EnemyoftheFarmer/DC-programmable-load/Eload-Horizon/Electronic-Load/pool/3d_models/cache/6d752bc3-29b3-45df-8cf2-1e3aacefbcc6/3d_models/connector/header/2.54mm/PinHeader_2x06_P2.54mm_Vertical.step

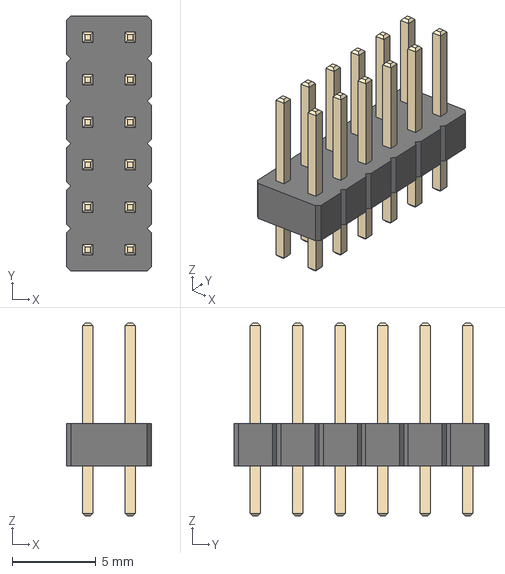
[picture p18: CAD file, 2022-11-15]
Eload-Horizon/Electronic-Load/pool/3d_models/cache/6d752bc3-29b3-45df-8cf2-1e3aacefbcc6/3d_models/connector/header/2.54mm/PinHeader_2x06_P2.54mm_Vertical.step
5.08 x 15.2 x 11.5 mm
