EnemyoftheFarmer/DC-programmable-load/Eload-Horizon/Electronic-Load/pool/3d_models/Mill-Max/mill-max-380-10-102-00-001000.STEP

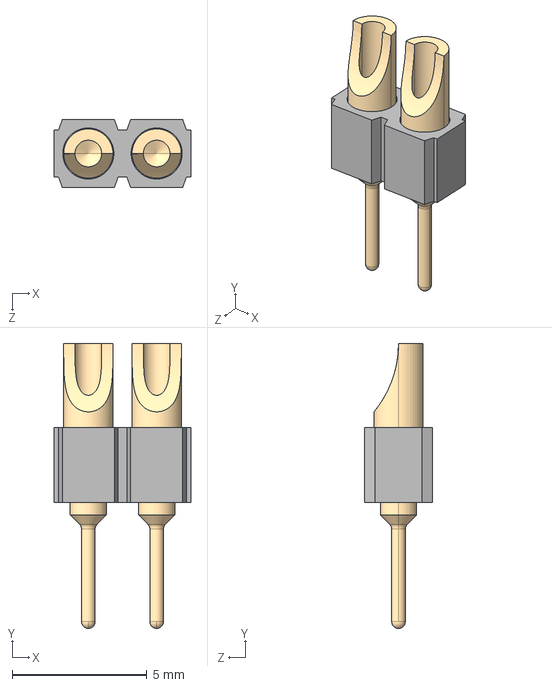
[picture p20: CAD file, 2022-11-15]
Eload-Horizon/Electronic-Load/pool/3d_models/Mill-Max/mill-max-380-10-102-00-001000.STEP
5.08 x 10.6 x 2.54 mm
P3XX-11-010-00-000000_P302-11-010-00-000000
