EnemyoftheFarmer/DC-programmable-load/Eload-Horizon/Electronic-Load/pool/3d_models/Vishay/thjp_3dmodels/THJP1206A.stp

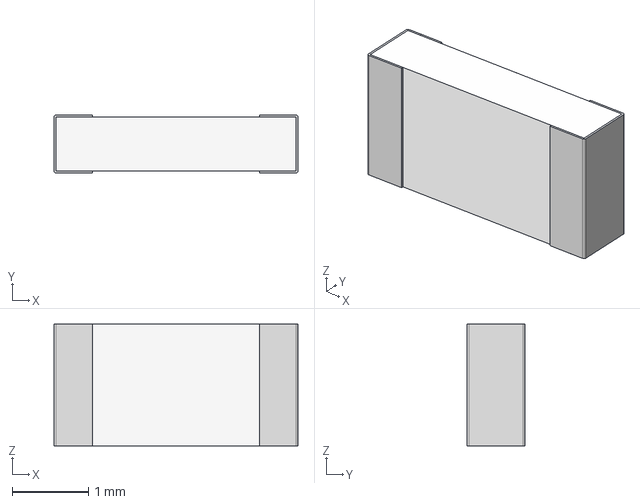
[picture p21: CAD file, 2022-04-26]
Eload-Horizon/Electronic-Load/pool/3d_models/Vishay/thjp_3dmodels/THJP1206A.stp
3.20 x 0.762 x 1.60 mm
