EnemyoftheFarmer/DC-programmable-load/Eload-Horizon/Electronic-Load/pool/3d_models/Vishay/WSL2010...18 (0.001 to 0.0069).STEP

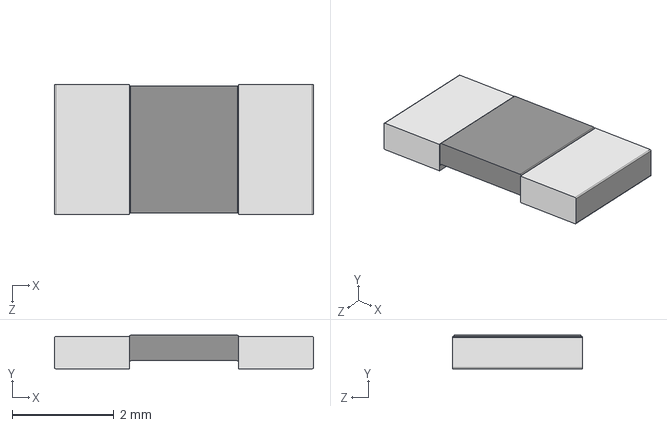
[picture p22: CAD file, 2022-04-26]
Eload-Horizon/Electronic-Load/pool/3d_models/Vishay/WSL2010...18 (0.001 to 0.0069).STEP
5.08 x 0.66 x 2.54 mm
