EnemyoftheFarmer/DC-programmable-load/Eload-Horizon/Controller/pool/3d_models/cache/6d752bc3-29b3-45df-8cf2-1e3aacefbcc6/3d_models/connector/header/2.54mm/PinHeader_1x04_P2.54mm_Vertical.step

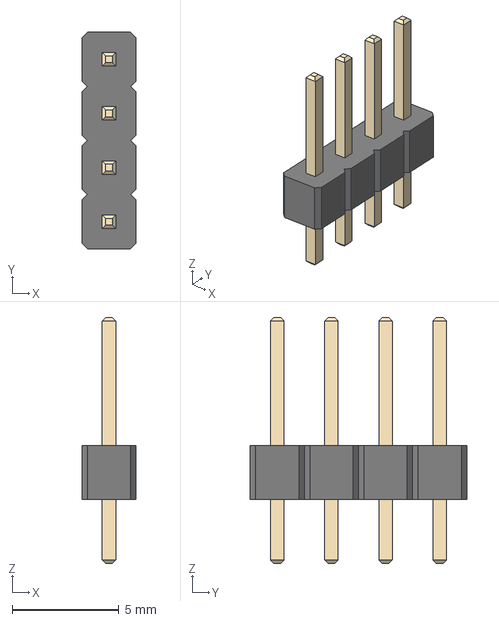
[picture p24: CAD file, 2022-11-15]
Eload-Horizon/Controller/pool/3d_models/cache/6d752bc3-29b3-45df-8cf2-1e3aacefbcc6/3d_models/connector/header/2.54mm/PinHeader_1x04_P2.54mm_Vertical.step
2.54 x 10.2 x 11.5 mm
