EnemyoftheFarmer/DC-programmable-load/Eload-Horizon/Electronic-Load/pool/3d_models/Vishay/RS1-2.STEP

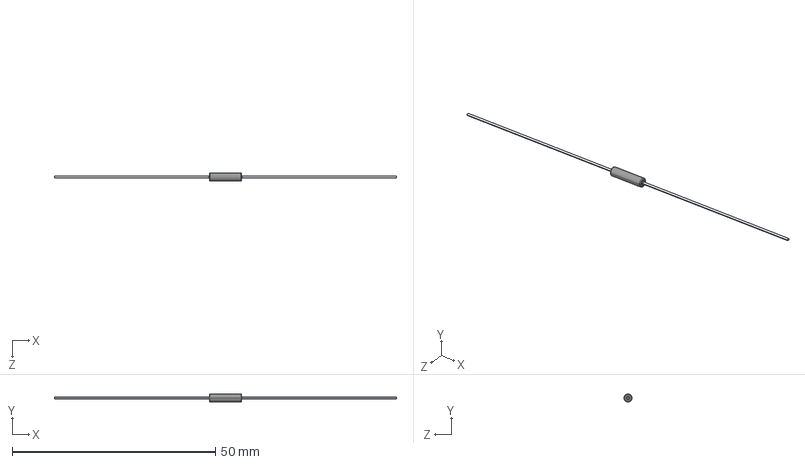
[picture p25: CAD file, 2022-04-26]
Eload-Horizon/Electronic-Load/pool/3d_models/Vishay/RS1-2.STEP
84.1 x 1.98 x 1.98 mm
