EnemyoftheFarmer/DC-programmable-load/Eload-Horizon/Electronic-Load/pool/3d_models/Vishay/thjp_3dmodels/THJP0612A.stp

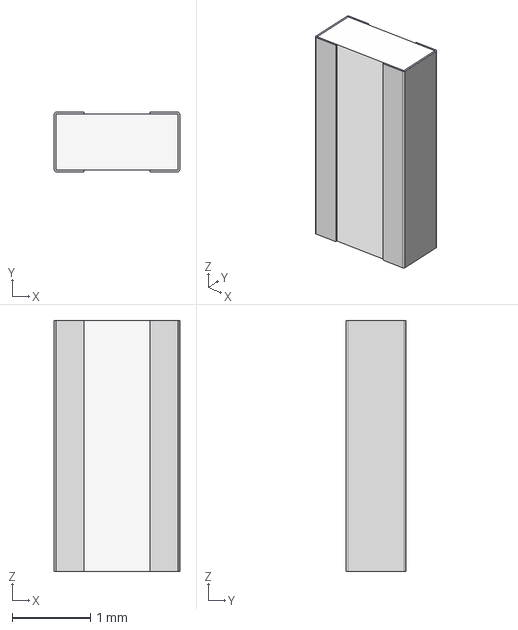
[picture p26: CAD file, 2022-04-26]
Eload-Horizon/Electronic-Load/pool/3d_models/Vishay/thjp_3dmodels/THJP0612A.stp
1.60 x 0.762 x 3.20 mm
