EnemyoftheFarmer/DC-programmable-load/Eload-Horizon/Split-Rail-Power-Supply/pool/3d_models/cache/6d752bc3-29b3-45df-8cf2-1e3aacefbcc6/3d_models/passive/capacitor/C_1206_3216Metric.step

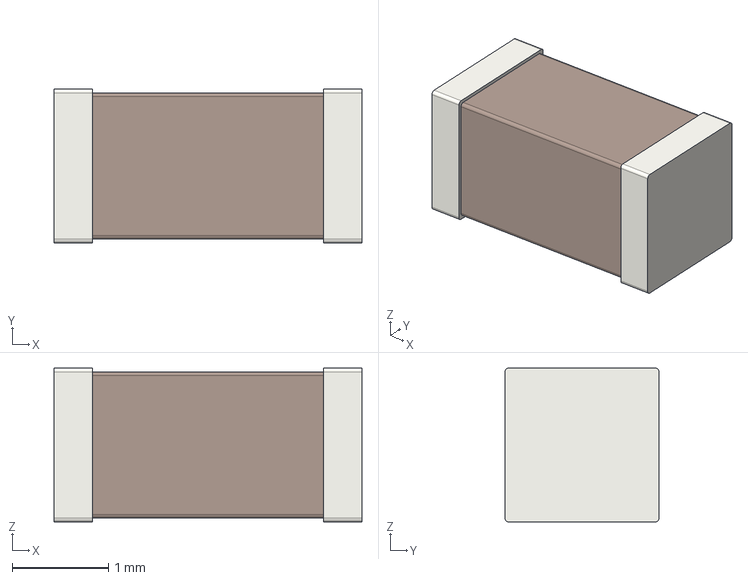
[picture p27: CAD file, 2022-11-15]
Eload-Horizon/Split-Rail-Power-Supply/pool/3d_models/cache/6d752bc3-29b3-45df-8cf2-1e3aacefbcc6/3d_models/passive/capacitor/C_1206_3216Metric.step
3.20 x 1.60 x 1.60 mm
