EnemyoftheFarmer/DC-programmable-load/Eload-Horizon/Electronic-Load/pool/3d_models/Vishay/CP0007...3.STEP

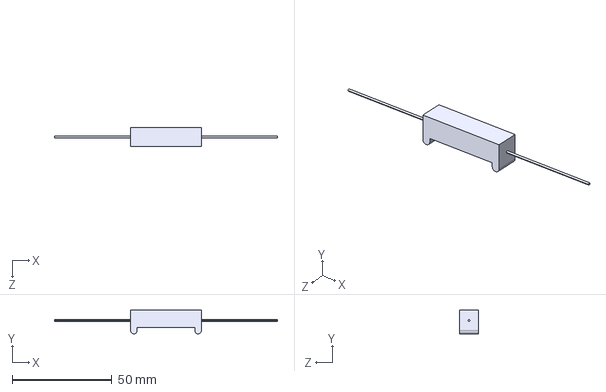
[picture p28: CAD file, 2022-04-26]
Eload-Horizon/Electronic-Load/pool/3d_models/Vishay/CP0007...3.STEP
111.5 x 11.9 x 9.52 mm
