EnemyoftheFarmer/DC-programmable-load/Eload-Horizon/Electronic-Load/pool/3d_models/Vishay/thjp_3dmodels/THJP0805A.stp

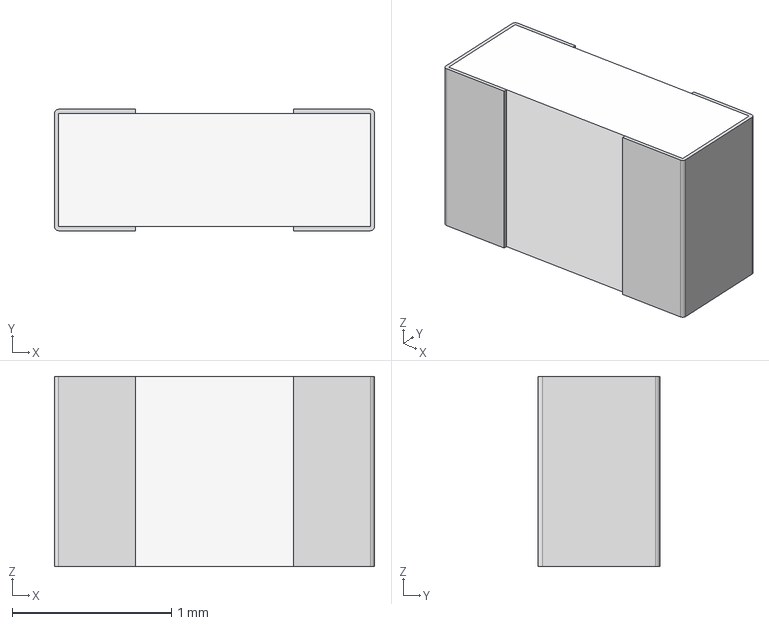
[picture p29: CAD file, 2022-04-26]
Eload-Horizon/Electronic-Load/pool/3d_models/Vishay/thjp_3dmodels/THJP0805A.stp
2.01 x 0.762 x 1.19 mm
