EnemyoftheFarmer/DC-programmable-load/Eload-Horizon/Electronic-Load/pool/3d_models/Vishay/CP0005.STEP

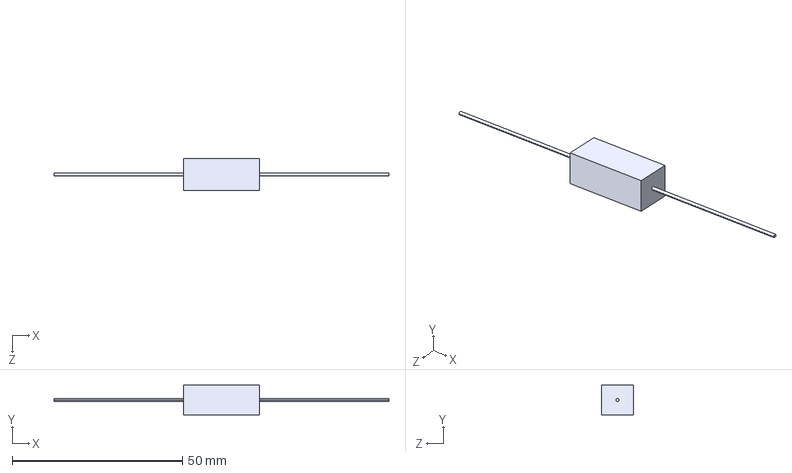
[picture p30: CAD file, 2022-04-26]
Eload-Horizon/Electronic-Load/pool/3d_models/Vishay/CP0005.STEP
98.4 x 8.73 x 9.52 mm
