EnemyoftheFarmer/DC-programmable-load/Eload-Horizon/Electronic-Load/pool/3d_models/Vishay/thjp_3dmodels/THJP0603A.stp

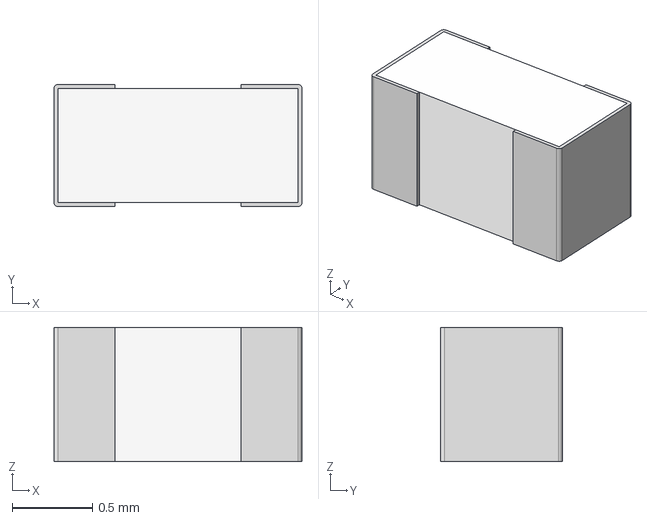
[picture p31: CAD file, 2022-04-26]
Eload-Horizon/Electronic-Load/pool/3d_models/Vishay/thjp_3dmodels/THJP0603A.stp
1.55 x 0.762 x 0.838 mm
