EnemyoftheFarmer/DC-programmable-load/Eload-Horizon/Electronic-Load/pool/3d_models/Vishay/CP0022.STEP

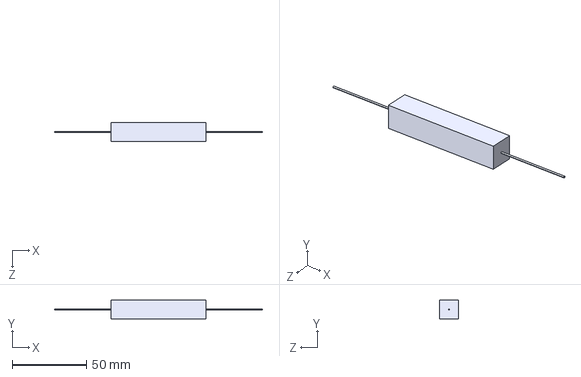
[picture p33: CAD file, 2022-04-26]
Eload-Horizon/Electronic-Load/pool/3d_models/Vishay/CP0022.STEP
139.7 x 12.7 x 12.7 mm
