EnemyoftheFarmer/DC-programmable-load/Eload-Horizon/Electronic-Load/pool/3d_models/Vishay/CP0025.STEP

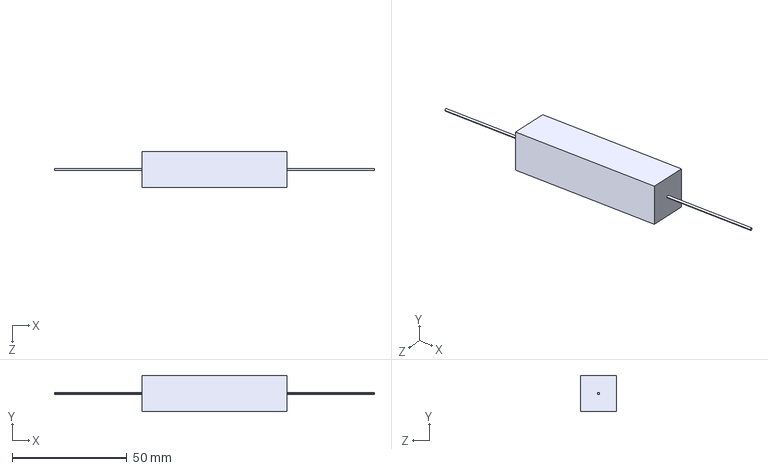
[picture p35: CAD file, 2022-04-26]
Eload-Horizon/Electronic-Load/pool/3d_models/Vishay/CP0025.STEP
139.7 x 15.9 x 15.9 mm
