EnemyoftheFarmer/DC-programmable-load/Eload-Horizon/Electronic-Load/pool/3d_models/Vishay/WSL2512...18 (0.007 to 0.04).stp

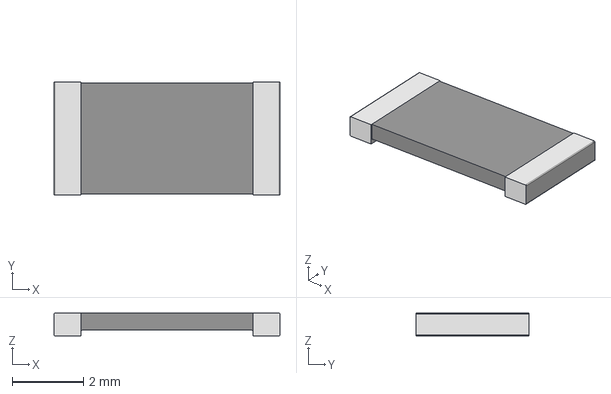
[picture p37: CAD file, 2022-04-26]
Eload-Horizon/Electronic-Load/pool/3d_models/Vishay/WSL2512...18 (0.007 to 0.04).stp
6.35 x 3.18 x 0.635 mm
