EnemyoftheFarmer/DC-programmable-load/Eload-Horizon/Electronic-Load/pool/3d_models/Vishay/CP0003.STEP

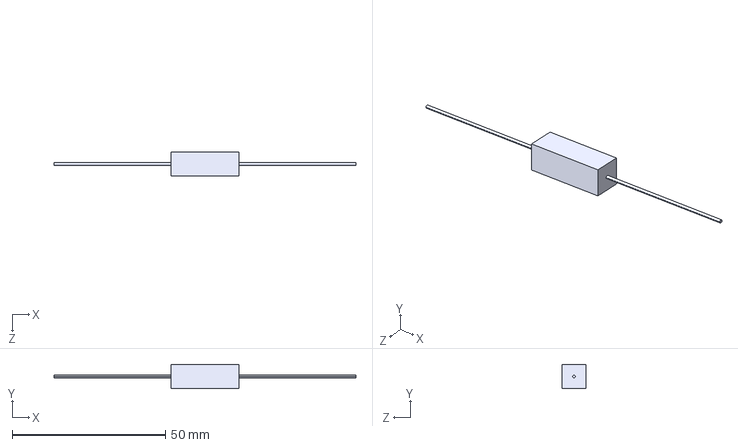
[picture p38: CAD file, 2022-04-26]
Eload-Horizon/Electronic-Load/pool/3d_models/Vishay/CP0003.STEP
98.4 x 7.94 x 7.94 mm
