EnemyoftheFarmer/DC-programmable-load/Eload-Horizon/Electronic-Load/pool/3d_models/Vishay/WSLP4026 (0.2mohm).stp

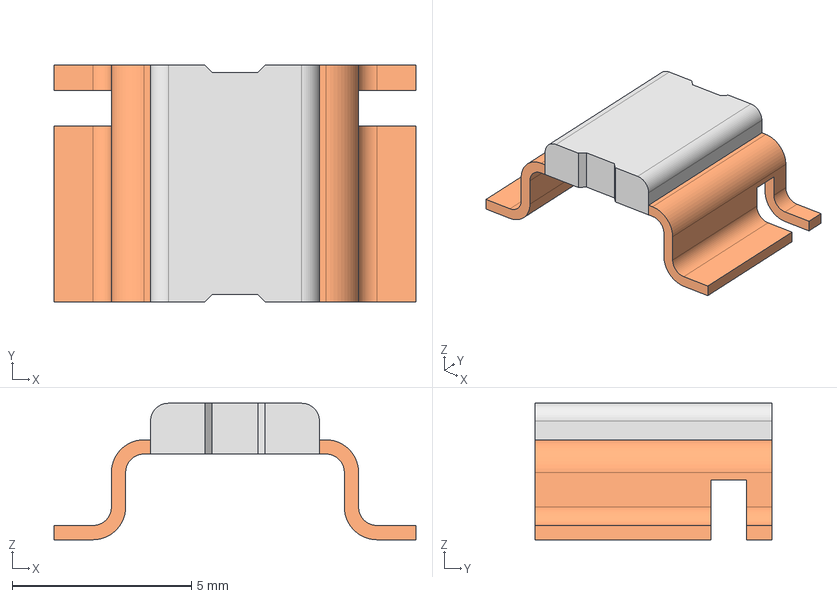
[picture p39: CAD file, 2022-04-26]
Eload-Horizon/Electronic-Load/pool/3d_models/Vishay/WSLP4026 (0.2mohm).stp
10.1 x 6.60 x 3.81 mm
