EnemyoftheFarmer/DC-programmable-load/Eload-Horizon/Electronic-Load/pool/3d_models/Vishay/RS01A.STEP

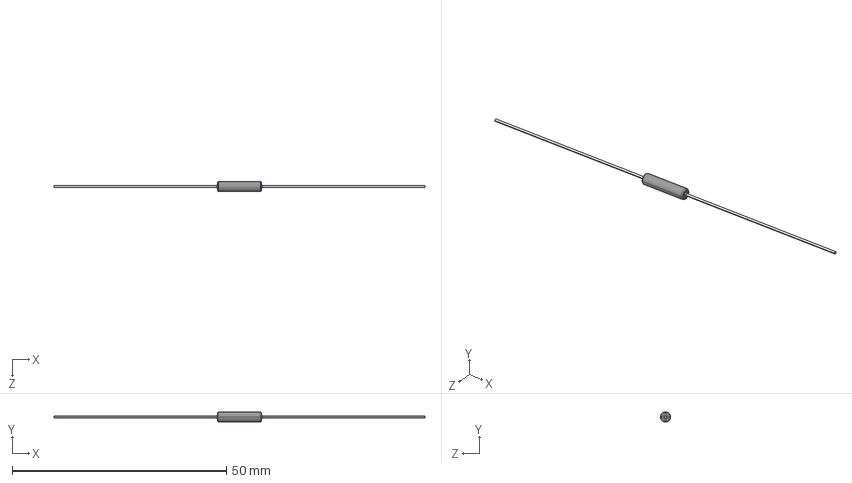
[picture p41: CAD file, 2022-04-26]
Eload-Horizon/Electronic-Load/pool/3d_models/Vishay/RS01A.STEP
86.5 x 2.39 x 2.39 mm
