EnemyoftheFarmer/DC-programmable-load/Eload-Horizon/Electronic-Load/pool/3d_models/Vishay/WSL0603...18 (0.01 to 0.1).STEP

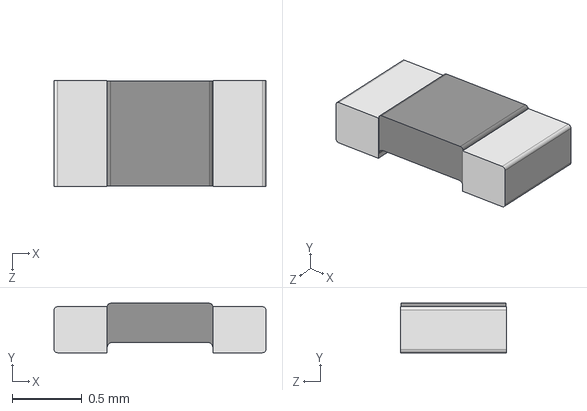
[picture p42: CAD file, 2022-04-26]
Eload-Horizon/Electronic-Load/pool/3d_models/Vishay/WSL0603...18 (0.01 to 0.1).STEP
1.52 x 0.355 x 0.76 mm
