EnemyoftheFarmer/DC-programmable-load/Eload-Horizon/Electronic-Load/pool/3d_models/Vishay/RS1-4.STEP

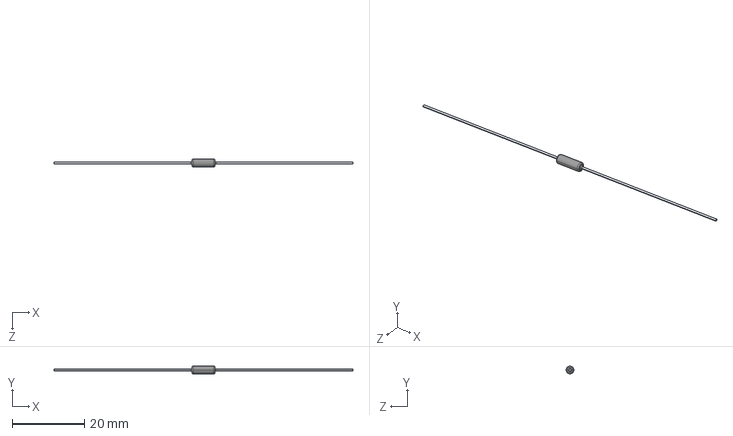
[picture p43: CAD file, 2022-04-26]
Eload-Horizon/Electronic-Load/pool/3d_models/Vishay/RS1-4.STEP
82.6 x 2.16 x 2.16 mm
