EnemyoftheFarmer/DC-programmable-load/Eload-Horizon/Electronic-Load/pool/3d_models/Vishay/RS02C...17.STEP

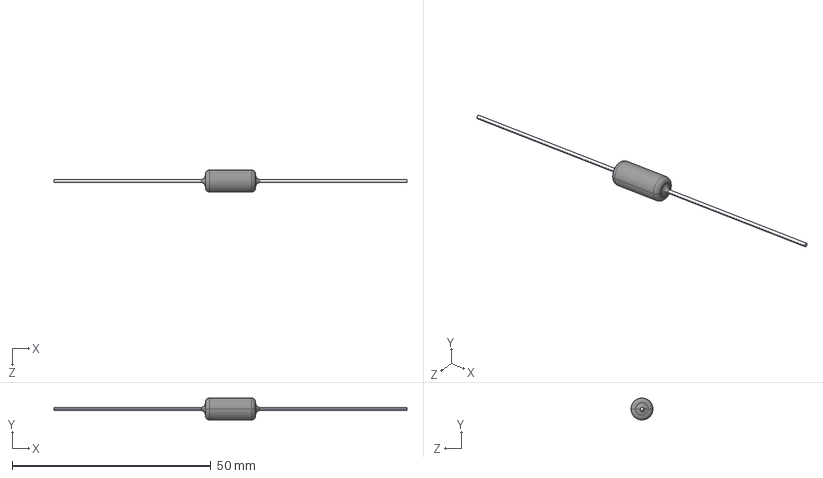
[picture p44: CAD file, 2022-04-26]
Eload-Horizon/Electronic-Load/pool/3d_models/Vishay/RS02C...17.STEP
88.9 x 5.54 x 5.54 mm
