EnemyoftheFarmer/DC-programmable-load/Eload-Horizon/Electronic-Load/pool/3d_models/Vishay/WSL2512...18 (0.0005 to 0.00099).STEP

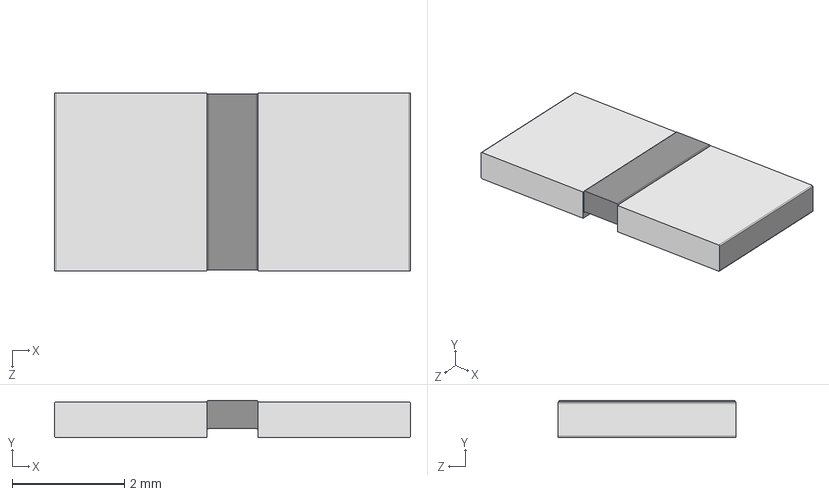
[picture p51: CAD file, 2022-04-26]
Eload-Horizon/Electronic-Load/pool/3d_models/Vishay/WSL2512...18 (0.0005 to 0.00099).STEP
6.35 x 0.66 x 3.18 mm
