EnemyoftheFarmer/DC-programmable-load/Eload-Horizon/Electronic-Load/pool/3d_models/Vishay/WSLP4026 (0.0003).STEP

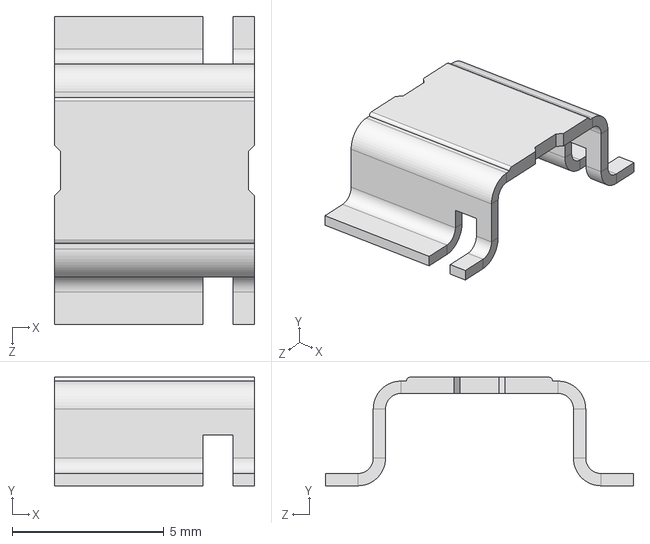
[picture p55: CAD file, 2022-04-26]
Eload-Horizon/Electronic-Load/pool/3d_models/Vishay/WSLP4026 (0.0003).STEP
6.60 x 3.58 x 10.2 mm
