EnemyoftheFarmer/DC-programmable-load/Eload-Horizon/Electronic-Load/pool/3d_models/Vishay/WSL1206...18 (0.001 to 0.0019).STEP

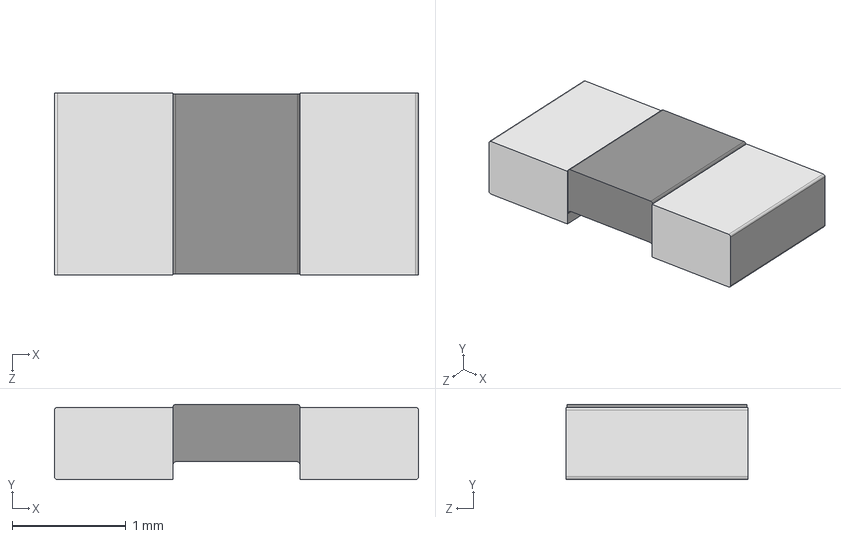
[picture p57: CAD file, 2022-04-26]
Eload-Horizon/Electronic-Load/pool/3d_models/Vishay/WSL1206...18 (0.001 to 0.0019).STEP
3.20 x 0.66 x 1.60 mm
