EnemyoftheFarmer/DC-programmable-load/Eload-Horizon/Electronic-Load/pool/3d_models/Vishay/WSL1206...18 (0.002 to 0.0059).stp

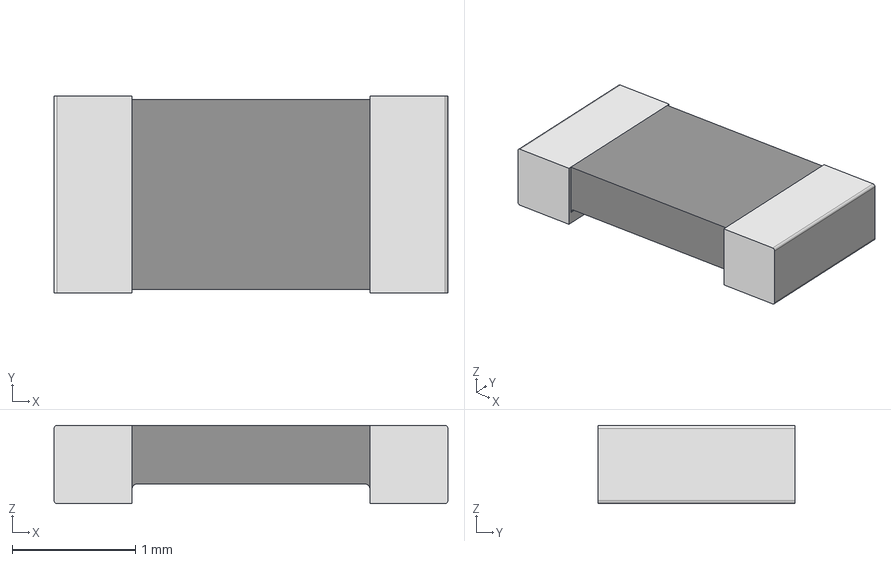
[picture p58: CAD file, 2022-04-26]
Eload-Horizon/Electronic-Load/pool/3d_models/Vishay/WSL1206...18 (0.002 to 0.0059).stp
3.20 x 1.60 x 0.635 mm
