EnemyoftheFarmer/DC-programmable-load/Eload-Horizon/Electronic-Load/pool/3d_models/Vishay/WSL0805...18 (0.005 to 0.2).STEP

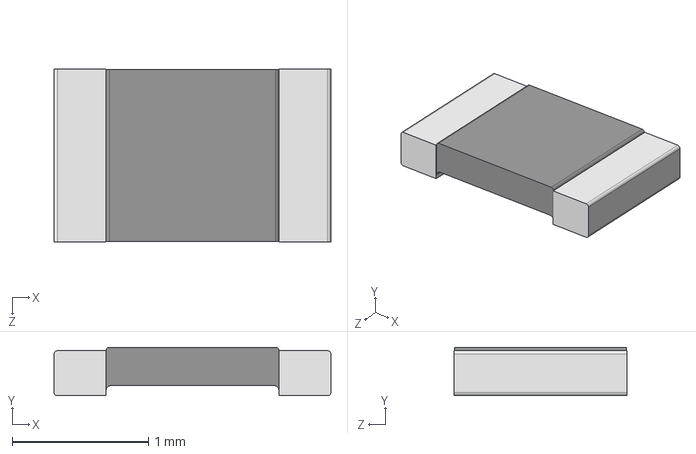
[picture p60: CAD file, 2022-04-26]
Eload-Horizon/Electronic-Load/pool/3d_models/Vishay/WSL0805...18 (0.005 to 0.2).STEP
2.03 x 0.355 x 1.27 mm
