EnemyoftheFarmer/DC-programmable-load/Eload-Horizon/Electronic-Load/pool/3d_models/Vishay/WSLP4026 (0.0005).stp

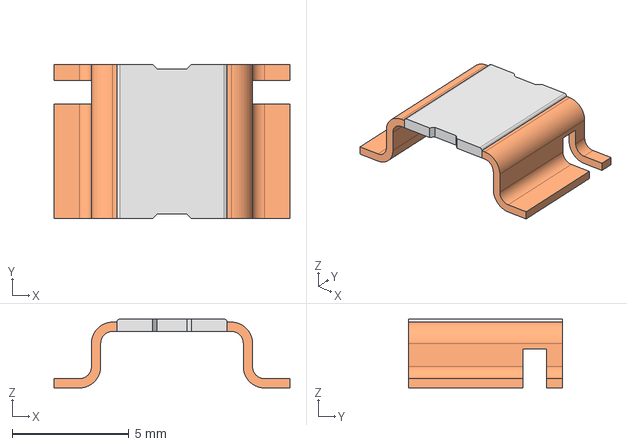
[picture p63: CAD file, 2022-04-26]
Eload-Horizon/Electronic-Load/pool/3d_models/Vishay/WSLP4026 (0.0005).stp
10.1 x 6.60 x 2.95 mm
