EnemyoftheFarmer/DC-programmable-load/Eload-Horizon/Electronic-Load/pool/3d_models/Vishay/WSL2010...18 (0.007 to 0.5).stp

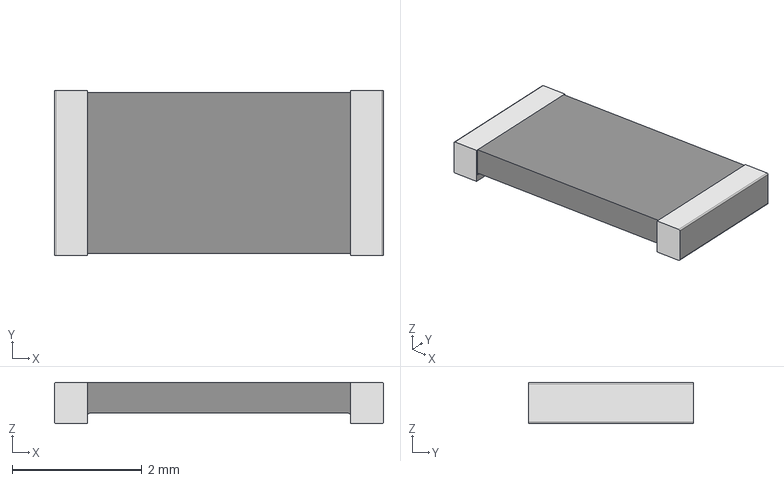
[picture p64: CAD file, 2022-04-26]
Eload-Horizon/Electronic-Load/pool/3d_models/Vishay/WSL2010...18 (0.007 to 0.5).stp
5.08 x 2.54 x 0.635 mm
